thestumbler/cage3d/datasheets/aluminum-2020-profile.jpg

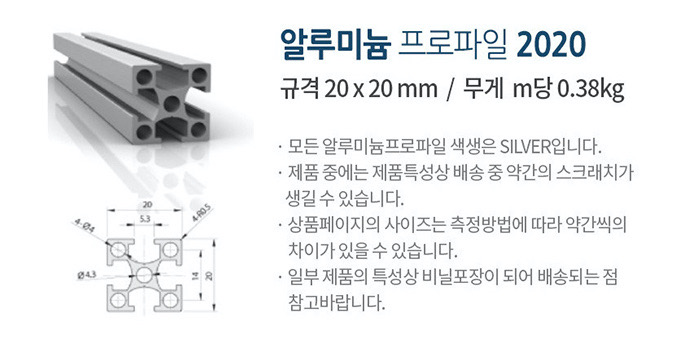
datasheets/aluminum-2020-profile.jpg
