thestumbler/cage3d/datasheets/hdw-corner-bracket-detail.jpg

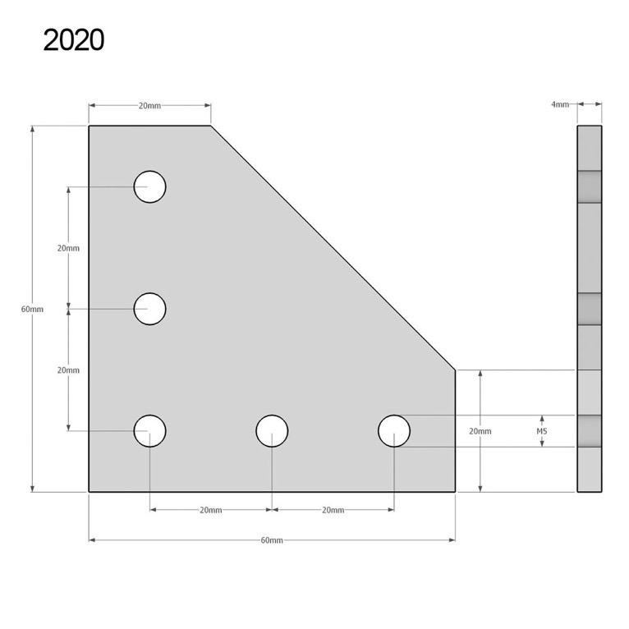
datasheets/hdw-corner-bracket-detail.jpg
